FRSname/charm-cam/Gallery/Charm-Cam-photo.png

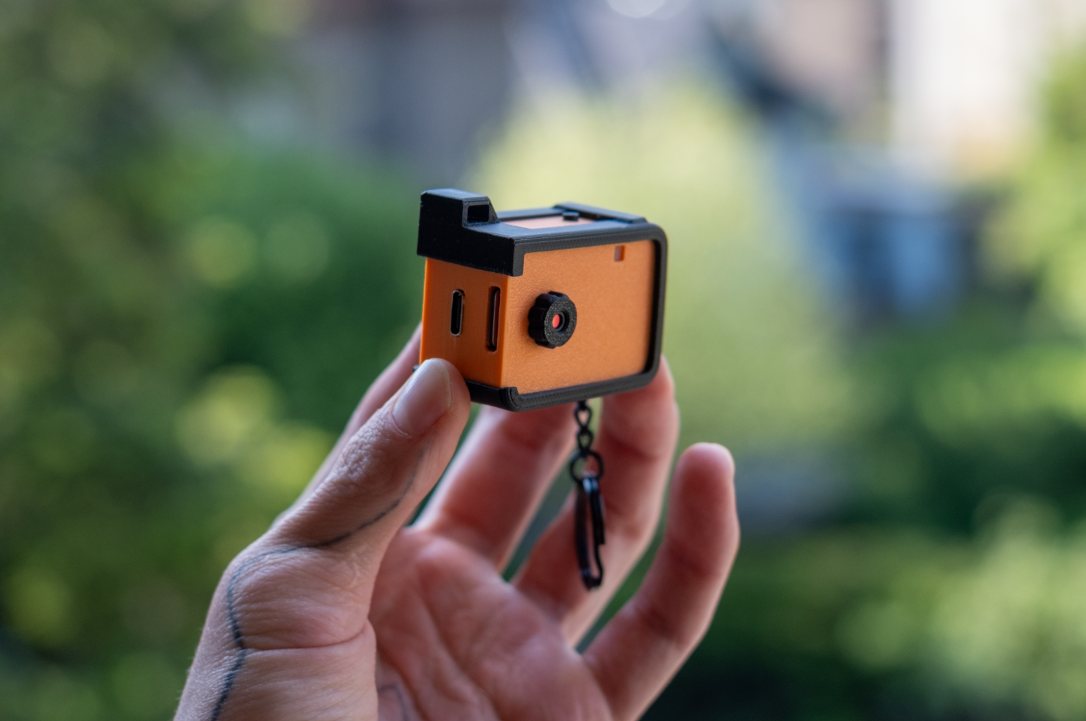
Gallery/Charm-Cam-photo.png
