FRSname/charm-cam/esp32cam_camera-v1.2/camera.ino

// ============================================================
// CAMERA INIT
// ============================================================

bool initCamera() {
  camera_config_t config = {};  // zero-init prevents crash from garbage
  config.ledc_channel = LEDC_CHANNEL_0;
  config.ledc_timer   = LEDC_TIMER_0;
  config.pin_d0       = Y2_GPIO_NUM;
  config.pin_d1       = Y3_GPIO_NUM;
  config.pin_d2       = Y4_GPIO_NUM;
  config.pin_d3       = Y5_GPIO_NUM;
  config.pin_d4       = Y6_GPIO_NUM;
  config.pin_d5       = Y7_GPIO_NUM;
  config.pin_d6       = Y8_GPIO_NUM;
  config.pin_d7       = Y9_GPIO_NUM;
  config.pin_xclk     = XCLK_GPIO_NUM;
  config.pin_pclk     = PCLK_GPIO_NUM;
  config.pin_vsync    = VSYNC_GPIO_NUM;
  config.pin_href     = HREF_GPIO_NUM;
  config.pin_sscb_sda = SIOD_GPIO_NUM;
  config.pin_sscb_scl = SIOC_GPIO_NUM;
  config.pin_pwdn     = PWDN_GPIO_NUM;
  config.pin_reset    = RESET_GPIO_NUM;
  config.xclk_freq_hz = 20000000;
  config.pixel_format = PIXFORMAT_JPEG;

  // UXGA (1600x1200) requires PSRAM — fall back to SVGA without it
  if (psramFound()) {
    config.frame_size   = FRAMESIZE_UXGA;
    config.jpeg_quality = 8;
    config.fb_count     = 2;
    Serial.println("PSRAM found — UXGA mode");
  } else {
    config.frame_size   = FRAMESIZE_SVGA;
    config.jpeg_quality = 10;
    config.fb_count     = 1;
    Serial.println("No PSRAM — SVGA fallback");
  }

  esp_err_t err = esp_camera_init(&config);
  if (err != ESP_OK) {
    Serial.printf("Camera init failed: 0x%x\n", err);
    return false;
  }

  // OV2640 default tuning
  sensor_t* s = esp_camera_sensor_get();
  s->set_vflip(s, 0);
  s->set_hmirror(s, 0);
  s->set_brightness(s, 1);
  s->set_saturation(s, 0);

  Serial.println("Camera initialised OK");
  return true;
}
